aungheainsoe-hub/Mechatronic-Positioner-Sponsored-by-Mass.-Eye-Ear-Infirmary/No. 8 Washer.SLDPRT

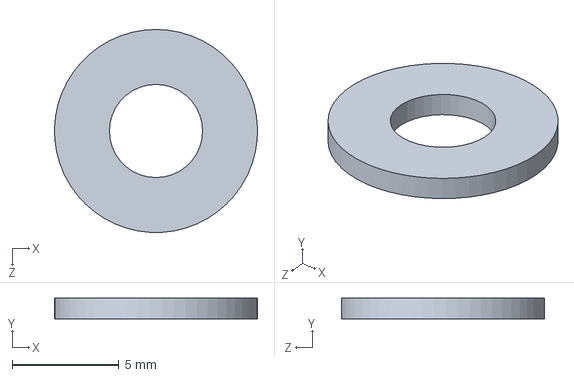
[picture p26: CAD file, 2026-06-21]
No. 8 Washer.SLDPRT
9.52 x 0.965 x 9.53 mm
