aungheainsoe-hub/Mechatronic-Positioner-Sponsored-by-Mass.-Eye-Ear-Infirmary/MM_92140A116_0.344x1.25_Flat-Washer.SLDPRT

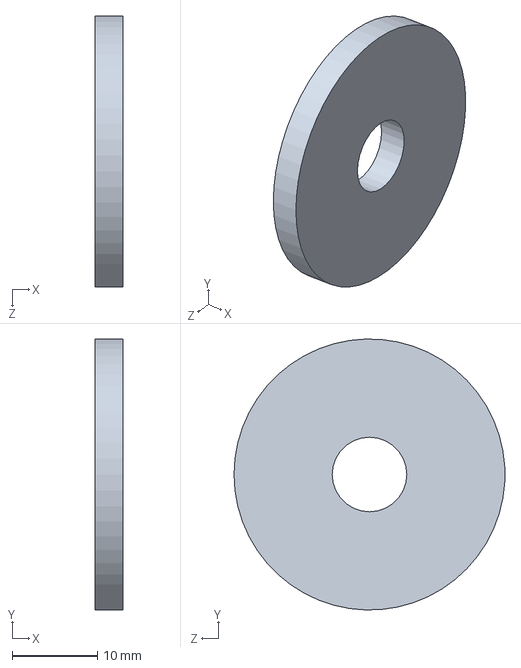
[picture p27: CAD file, 2026-06-21]
MM_92140A116_0.344x1.25_Flat-Washer.SLDPRT
3.30 x 31.7 x 31.8 mm
