aungheainsoe-hub/Mechatronic-Positioner-Sponsored-by-Mass.-Eye-Ear-Infirmary/MM_92150A137_0.515IDx0.875OD_Plastic-Washer.SLDPRT

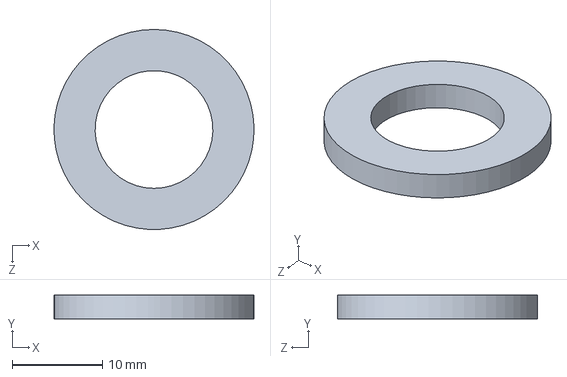
[picture p28: CAD file, 2026-06-21]
MM_92150A137_0.515IDx0.875OD_Plastic-Washer.SLDPRT
22.2 x 2.64 x 22.2 mm
