aungheainsoe-hub/Mechatronic-Positioner-Sponsored-by-Mass.-Eye-Ear-Infirmary/MM_94902A101_0.25-20_Flange-Nut.SLDPRT

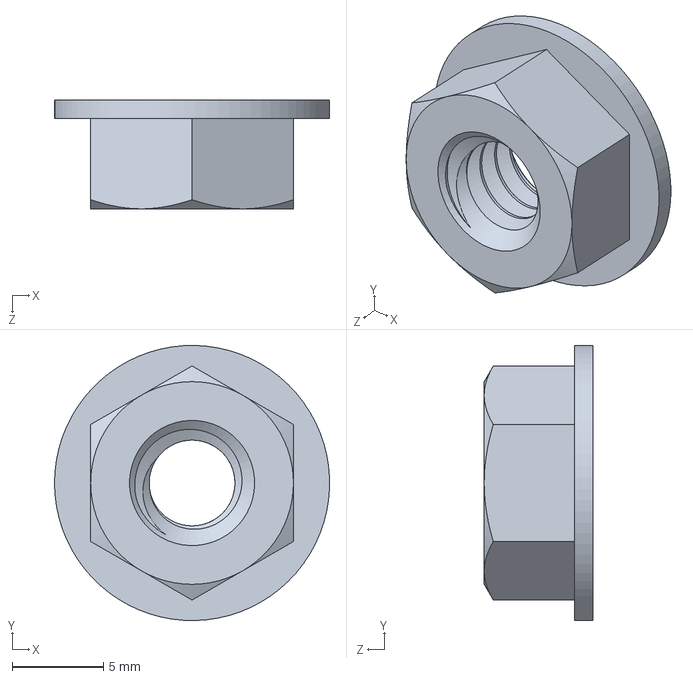
[picture p29: CAD file, 2026-06-21]
MM_94902A101_0.25-20_Flange-Nut.SLDPRT
15.1 x 15.1 x 5.95 mm
